PrinceOfDuloc/NightGlow/Experiments/4. Ambient Light Sensor Electrical Characteristics (External DC Supply)/4.1.0 - Light Sensor Step Change Response (low amplification).png

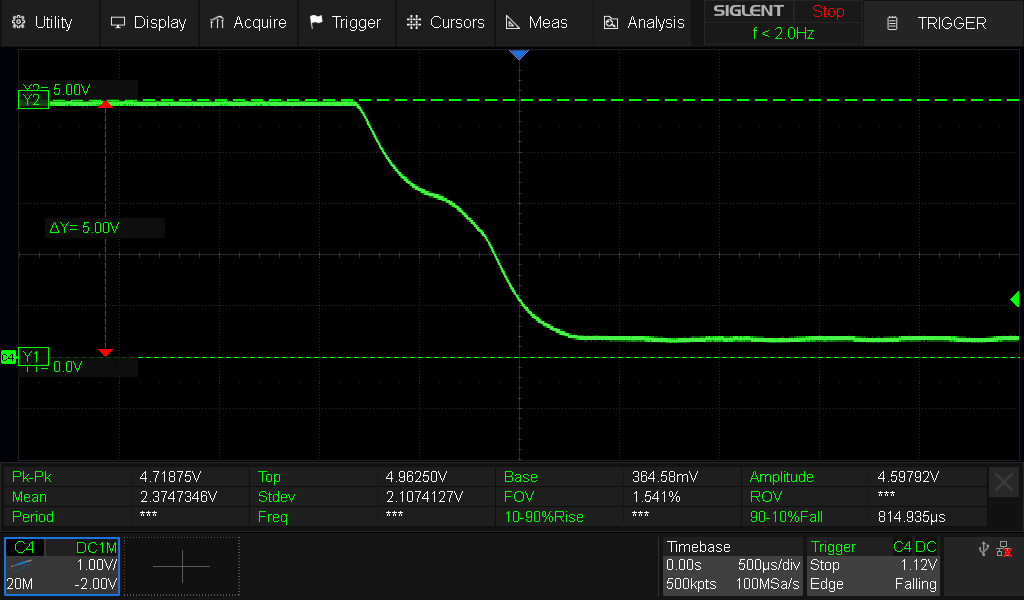
Experiments/4. Ambient Light Sensor Electrical Characteristics (External DC Supply)/4.1.0 - Light Sensor Step Change Response (low amplification).png
