PrinceOfDuloc/NightGlow/Experiments/Other/PFC using just an inductor/Load = 7.3k, L = 0 (shorted).png

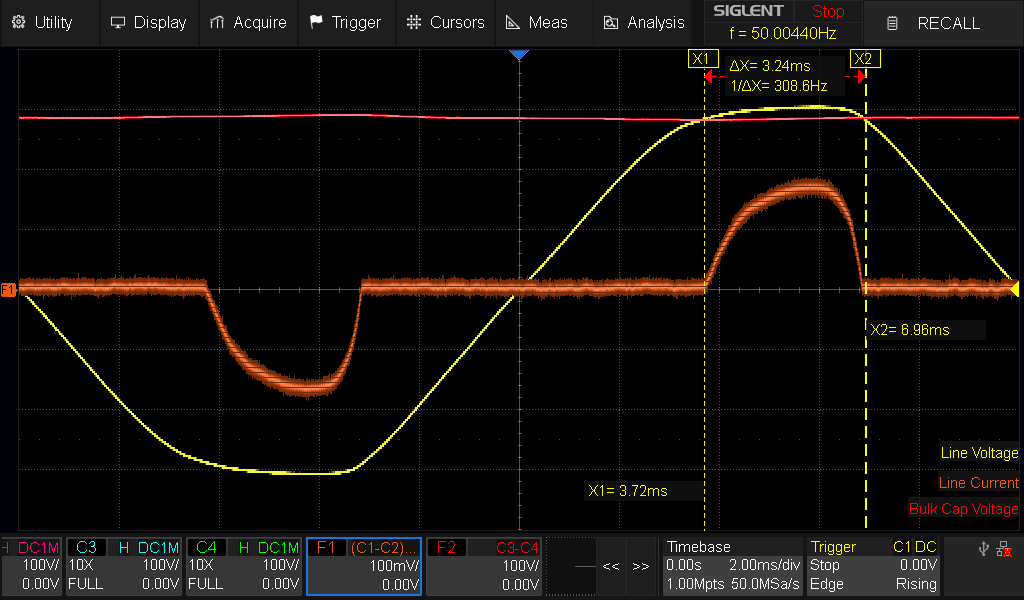
Experiments/Other/PFC using just an inductor/Load = 7.3k, L = 0 (shorted).png
