PrinceOfDuloc/NightGlow/Experiments/Other/PFC using just an inductor/Load = 22k, L = 0 (shorted).png

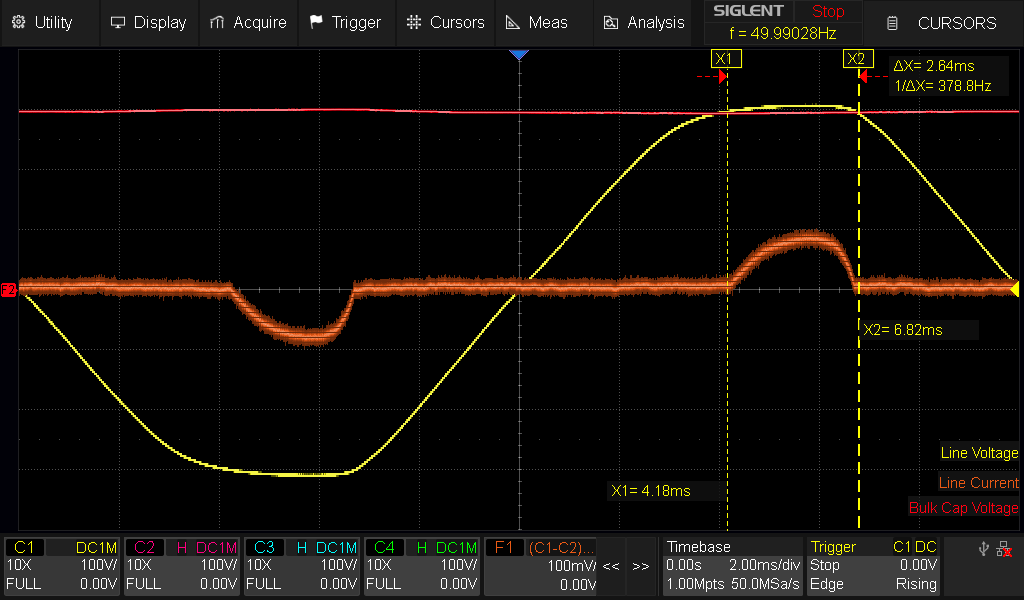
Experiments/Other/PFC using just an inductor/Load = 22k, L = 0 (shorted).png
