PrinceOfDuloc/NightGlow/Experiments/Other/PFC using just an inductor/Physical Circuit.jpg

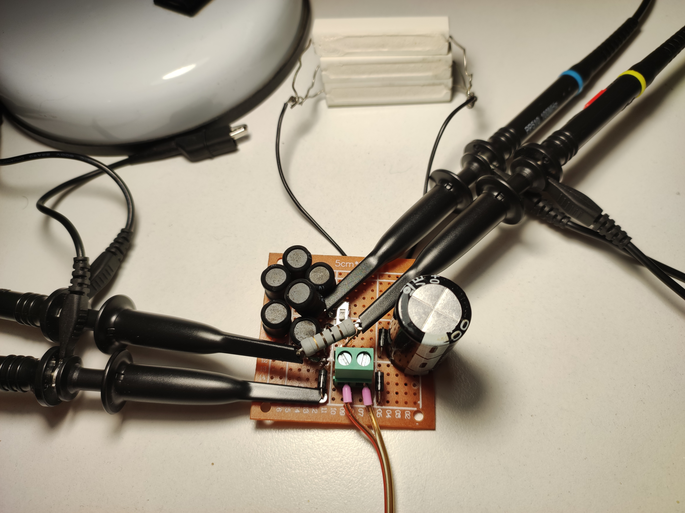
Experiments/Other/PFC using just an inductor/Physical Circuit.jpg
