PrinceOfDuloc/NightGlow/Experiments/Other/PFC using just an inductor/PFC using just an inductor.kicad_sch

## KiCad design Experiments/Other/PFC using just an inductor/PFC using just an inductor.kicad_sch (2026-08-19)

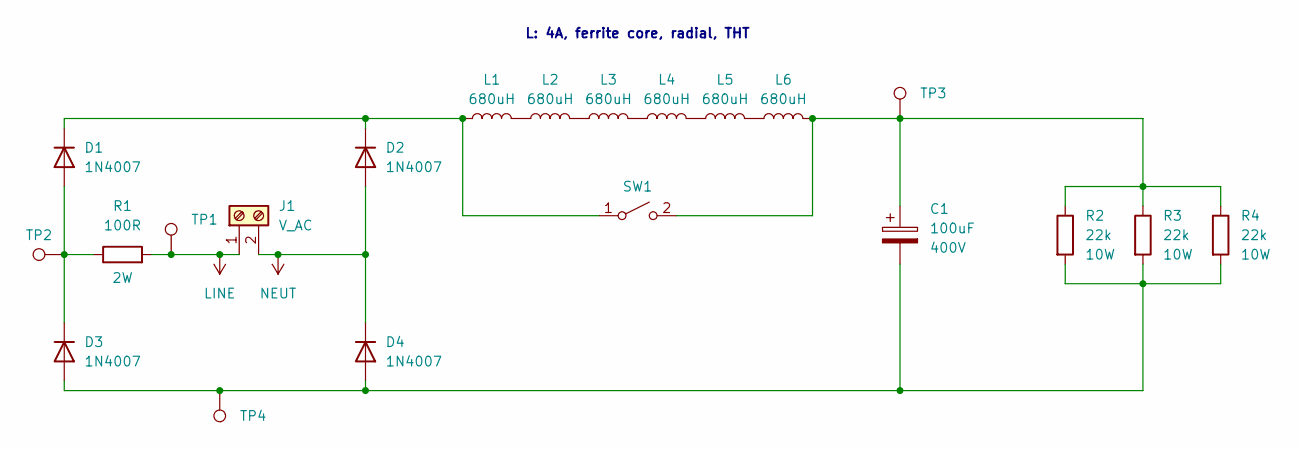
[picture p49: schematic PFC using just an inductor.kicad_sch]

Parts:
C1: 100uF
D1, D2, D3, D4: 1N4007; D_DO-41_SOD81_P10.16mm_Horizontal
J1: V_AC
L1, L2, L3, L4, L5, L6: 680uH
R1: 100R
R2, R3, R4: 22k
SW1: SW_SPST
TP1, TP2, TP3, TP4: TestPoint

Connections:
LINE: J1.1, R1.2, TP1.1
NEUT: D2.2 (A), D4.1 (K), J1.2
unnamed: C1.1, L6.2, R2.1, R3.1, R4.1, SW1.2 (B), TP3.1
unnamed: C1.2, D3.2 (A), D4.2 (A), R2.2, R3.2, R4.2, TP4.1
unnamed: D1.1 (K), D2.1 (K), L1.1, SW1.1 (A)
unnamed: D1.2 (A), D3.1 (K), R1.1, TP2.1
unnamed: L1.2, L2.1
unnamed: L2.2, L3.1
unnamed: L3.2, L4.1
unnamed: L4.2, L5.1
unnamed: L5.2, L6.1

Notes on the sheet:
L: 4A, ferrite core, radial, THT
