PrinceOfDuloc/NightGlow/Experiments/6. Capacitive Dropper Regulation/6.0 Bench Test Setup.jpg

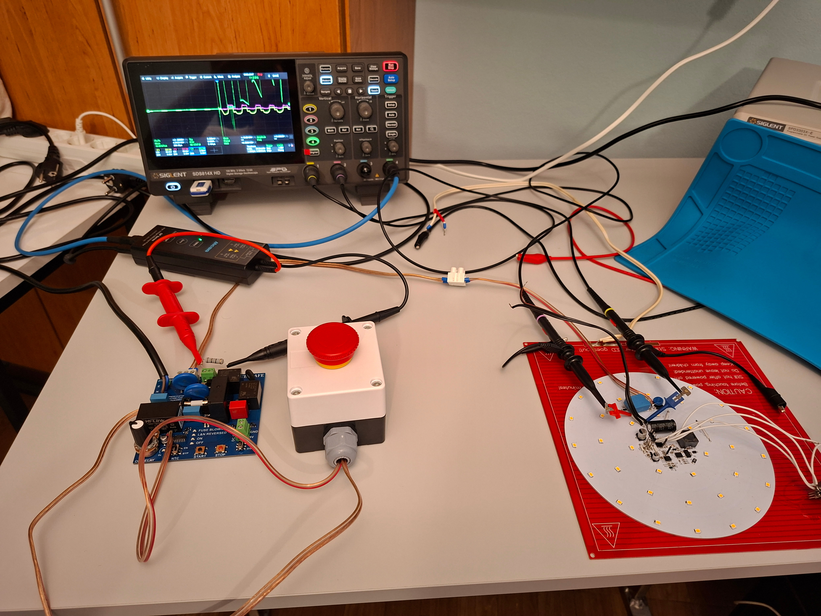
Experiments/6. Capacitive Dropper Regulation/6.0 Bench Test Setup.jpg
